KoJZz/Control-Rakatuy/testing/testing.kicad_sch

## KiCad design testing/testing.kicad_sch (2026-04-11)

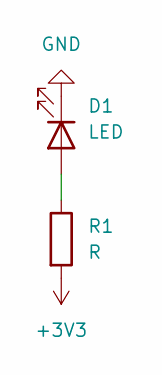
[picture p53: schematic testing.kicad_sch]

Parts:
D1: LED
R1: R

Connections:
+3V3: R1.2
GND: D1.1 (K)
unnamed: D1.2 (A), R1.1
