KoJZz/Control-Rakatuy/Firmware/FOCCube/Core/Src/main.c

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
/* Includes ------------------------------------------------------------------*/
#include "main.h"
#include "usb_device.h"

/* USER CODE BEGIN Includes */
#include "main.h"
#include "usb_device.h"
#include "usbd_cdc_if.h" // For CDC_Transmit_FS
#include "arm_math.h"
#include <stdbool.h>
#include <stdio.h>       // For snprintf
/* USER CODE END Includes */

ADC_HandleTypeDef hadc1;
ADC_HandleTypeDef hadc2;

TIM_HandleTypeDef htim1;
TIM_HandleTypeDef htim2;

/* USER CODE BEGIN PV */
extern volatile bool hardware_fault_latched;
extern volatile float32_t current_vbus_v;
extern volatile float32_t system_max_voltage;
extern volatile float32_t target_Id;
extern volatile float32_t target_Iq;
extern volatile float32_t offset_a;
extern volatile float32_t offset_c;

extern volatile float32_t I_q;
extern volatile float32_t I_d;
extern volatile float current_velocity_rad_s;
extern volatile float base_electrical_angle;

volatile float serial_commanded_current = 0.0f; // Stores the USB input


/* USER CODE END PV */

void SystemClock_Config(void);
static void MX_GPIO_Init(void);
static void MX_ADC1_Init(void);
static void MX_TIM1_Init(void);
static void MX_ADC2_Init(void);
static void MX_TIM2_Init(void);
/**
  * @brief  The application entry point.
  * @retval int
  */
int main(void)
{

  /* MCU Configuration--------------------------------------------------------*/

  /* Reset of all peripherals, Initializes the Flash interface and the Systick. */
  HAL_Init();

  /* Configure the system clock */
  SystemClock_Config();

  /* Initialize all configured peripherals */
  MX_GPIO_Init();
  MX_ADC1_Init();
  MX_TIM1_Init();
  MX_USB_DEVICE_Init();
  MX_ADC2_Init();
  MX_TIM2_Init();
  /* USER CODE BEGIN 2 */
  // 1. Enable Gate Driver
  HAL_GPIO_WritePin(EN_GATE_GPIO_Port, EN_GATE_Pin, GPIO_PIN_SET);
  HAL_Delay(10);

  // 2. Start ADCs
  HAL_ADCEx_InjectedStart(&hadc1);
  HAL_ADCEx_InjectedStart(&hadc2);

  // ==========================================
  // 3. DC CALIBRATION (Find true 0-Amp midpoint)
  // ==========================================
  HAL_GPIO_WritePin(EN_GATE_GPIO_Port, EN_GATE_Pin, GPIO_PIN_RESET);
  HAL_GPIO_WritePin(DC_CAL_GPIO_Port, DC_CAL_Pin, GPIO_PIN_SET);
  HAL_Delay(10);

  // CRITICAL FIX: Temporarily disable hardware triggers (JEXTEN = 00)
  // so the ADC respects our software JSWSTART command!
  hadc1.Instance->CR2 &= ~ADC_CR2_JEXTEN;
  hadc2.Instance->CR2 &= ~ADC_CR2_JEXTEN;

  uint32_t sum_a = 0, sum_c = 0;
  for(int i = 0; i < 1000; i++) {
	// Clear the JEOC flags BEFORE starting the conversion
	hadc1.Instance->SR = ~(ADC_SR_JEOC);
	hadc2.Instance->SR = ~(ADC_SR_JEOC);

	// Trigger BOTH ADCs manually
	SET_BIT(hadc1.Instance->CR2, ADC_CR2_JSWSTART);
	SET_BIT(hadc2.Instance->CR2, ADC_CR2_JSWSTART);

	while (!(hadc1.Instance->SR & ADC_SR_JEOC)) {}
	while (!(hadc2.Instance->SR & ADC_SR_JEOC)) {}

	sum_a += HAL_ADCEx_InjectedGetValue(&hadc1, ADC_INJECTED_RANK_1);
	sum_c += HAL_ADCEx_InjectedGetValue(&hadc2, ADC_INJECTED_RANK_1);
	HAL_Delay(1);
  }

  extern volatile float32_t offset_a;
  extern volatile float32_t offset_c;
  offset_a = (float32_t)sum_a / 1000.0f;
  offset_c = (float32_t)sum_c / 1000.0f;

  HAL_GPIO_WritePin(DC_CAL_GPIO_Port, DC_CAL_Pin, GPIO_PIN_RESET);
  HAL_GPIO_WritePin(EN_GATE_GPIO_Port, EN_GATE_Pin, GPIO_PIN_SET);
  HAL_Delay(10);

  // ==========================================
  // 4. INITIALIZE PWM AND HARDWARE TIMERS
  // ==========================================
  // Pre-center the PWM registers at 50% (0V output) before turning them on
  TIM1->CCR1 = 2099;
  TIM1->CCR2 = 2099;
  TIM1->CCR3 = 2099;

  HAL_TIM_PWM_Start(&htim1, TIM_CHANNEL_1);
  HAL_TIMEx_PWMN_Start(&htim1, TIM_CHANNEL_1);
  HAL_TIM_PWM_Start(&htim1, TIM_CHANNEL_2);
  HAL_TIMEx_PWMN_Start(&htim1, TIM_CHANNEL_2);
  HAL_TIM_PWM_Start(&htim1, TIM_CHANNEL_3);
  HAL_TIMEx_PWMN_Start(&htim1, TIM_CHANNEL_3);

  extern void Init_Rotor_Angle(void);
  Init_Rotor_Angle();
  HAL_TIM_Base_Start(&htim2);

  // ==========================================
  // 5. ARM THE FOC LOOP
  // ==========================================
  // CRITICAL FIX: Restore the hardware triggers to Rising Edge (JEXTEN = 01)
  // so TIM1_CC4 can physically trigger the ADCs again.
  hadc1.Instance->CR2 |= ADC_EXTERNALTRIGINJECCONVEDGE_RISING;
  hadc2.Instance->CR2 |= ADC_EXTERNALTRIGINJECCONVEDGE_RISING;

  // Stop the ADCs from software mode, then restart them in Hardware Trigger mode
  HAL_ADC_Stop(&hadc1);
  HAL_ADC_Stop(&hadc2);
  HAL_ADCEx_InjectedStart(&hadc2);
  HAL_ADCEx_InjectedStart_IT(&hadc1);       // ARMS THE 20kHz INTERRUPT
  HAL_TIM_PWM_Start(&htim1, TIM_CHANNEL_4); // STARTS FIRING THE ADC TRIGGER
  /* USER CODE END 2 */

  /* Infinite loop */
  /* USER CODE BEGIN WHILE */
  while (1)
  {
	uint16_t raw_throttle = 0;
	uint16_t raw_vbus = 0;
	// ========================================================
	// 1. POLL REGULAR ADC CHANNELS (Register-Level Multiplexing)
	// ========================================================
	uint32_t timeout;

	// Force the Sequence Length to exactly 1 conversion
	hadc1.Instance->SQR1 &= ~ADC_SQR1_L;

	// --- Read Throttle (Channel 5) ---
	hadc1.Instance->SQR3 = 5; // Tell the sequencer to only look at CH5
	SET_BIT(hadc1.Instance->CR2, ADC_CR2_SWSTART);

	timeout = 20000;
	while (!(hadc1.Instance->SR & ADC_SR_EOC) && --timeout) {}

	if (timeout > 0) {
	  raw_throttle = hadc1.Instance->DR;
	} else {
	  hadc1.Instance->SR = ~ADC_SR_OVR; // Clear Overrun if interrupted
	}

	// --- Read Battery Voltage (Channel 12) ---
	hadc1.Instance->SQR3 = 12; // Tell the sequencer to only look at CH12
	SET_BIT(hadc1.Instance->CR2, ADC_CR2_SWSTART);

	timeout = 20000;
	while (!(hadc1.Instance->SR & ADC_SR_EOC) && --timeout) {}

	if (timeout > 0) {
	  raw_vbus = hadc1.Instance->DR;

	  float32_t instant_vbus = (float32_t)raw_vbus * 0.015091f;
	  current_vbus_v = (current_vbus_v * 0.99f) + (instant_vbus * 0.01f);
	  system_max_voltage = current_vbus_v / 1.73205081f;
	} else {
	  hadc1.Instance->SR = ~ADC_SR_OVR;
	}

	// ========================================================
	// 3. THROTTLE MAPPING & SAFETY INTERLOCKS
	// ========================================================
	// TEST FLAGS: Change these during development
	bool bypass_deadman = true;

	static uint32_t fault_timer = 0;
	static bool in_fault_recovery = false;

	uint8_t deadman_pressed = (HAL_GPIO_ReadPin(DEADMAN_GPIO_Port, DEADMAN_Pin) == GPIO_PIN_RESET) || bypass_deadman;
	uint8_t voltage_safe = (current_vbus_v > 40.0f && current_vbus_v < 55.0f);

	// --- SCENARIO 1: HARDWARE FAULT DETECTED ---
	// We now read our software latch instead of the physical pin!
	uint8_t drv_faulted = hardware_fault_latched;

	if (drv_faulted || in_fault_recovery)
	{
	  target_Iq = 0.0f; // Immediately kill software torque
	  HAL_GPIO_WritePin(LED_GREEN_GPIO_Port, LED_GREEN_Pin, GPIO_PIN_RESET);
	  HAL_GPIO_WritePin(LED_RED_GPIO_Port, LED_RED_Pin, GPIO_PIN_SET);

	  if (!in_fault_recovery) {
		  fault_timer = HAL_GetTick();
		  in_fault_recovery = true;
	  }
	  else if (HAL_GetTick() - fault_timer > 2000) {

		  extern void Reset_FOC_Integrators(void);
		  Reset_FOC_Integrators();

		  extern void Init_Rotor_Angle(void);
		  Init_Rotor_Angle();

		  // --- WAKE UP SEQUENCE ---
		  hardware_fault_latched = false;                 // 1. Clear the latch
		  TIM1->BDTR |= TIM_BDTR_MOE;                     // 2. Restore PWM outputs
		  HAL_GPIO_WritePin(EN_GATE_GPIO_Port, EN_GATE_Pin, GPIO_PIN_SET); // 3. Enable Gates

		  in_fault_recovery = false;
	  }
	}
	// --- SCENARIO 2: SYSTEM NORMAL & ARMED ---
	else if (deadman_pressed && voltage_safe)
	{
	  HAL_GPIO_WritePin(LED_GREEN_GPIO_Port, LED_GREEN_Pin, GPIO_PIN_SET);
	  HAL_GPIO_WritePin(LED_RED_GPIO_Port, LED_RED_Pin, GPIO_PIN_RESET);

	  /* --- TEMPORARILY DISABLED FOR SERIAL BENCH TEST ---
	  float32_t commanded_current = 0.0f;
	  if (raw_throttle > 1000) {
		  commanded_current = ((float32_t)(raw_throttle - 1000) / 2000.0f) * 20.0f;
		  if (commanded_current > 20.0f) commanded_current = 20.0f;
	  }
	  target_Iq = commanded_current;
	  --------------------------------------------------- */

	  target_Iq = serial_commanded_current; // Feed FOC from USB instead
	}
	// --- SCENARIO 3: SYSTEM SAFE (IDLE) ---
	else
	{
	  HAL_GPIO_WritePin(LED_GREEN_GPIO_Port, LED_GREEN_Pin, GPIO_PIN_RESET);
	  HAL_GPIO_WritePin(LED_RED_GPIO_Port, LED_RED_Pin, GPIO_PIN_SET);
	  target_Iq = 0.0f;
	}
	// ========================================================
	// 4. USB TELEMETRY STREAM (10Hz)
	// ========================================================
	static uint32_t last_print_time = 0;

	// Print every 100ms so it is readable by a human
	if (HAL_GetTick() - last_print_time >= 100)
	{
	  last_print_time = HAL_GetTick();

	  // Create a character buffer to hold the formatted string
	  static char telemetry_buffer[128];

	  // Format the string with your live FOC metrics
	  // \r\n acts as the "Enter" key for the serial terminal
	  uint16_t len = snprintf(telemetry_buffer, sizeof(telemetry_buffer),
							  "Vbus:%5.1fV | RPM:%6.0f | Tgt:%5.2fA | Iq:%5.2fA | Id:%5.2fA\r\n",
							  current_vbus_v,
							  (current_velocity_rad_s * 9.549297f) / POLE_PAIRS, // Convert rad/s to mechanical RPM
							  target_Iq,
							  I_q,
							  I_d);

	  // Fire it out of the USB port
	  CDC_Transmit_FS((uint8_t*)telemetry_buffer, len);
	}
	// Run the main loop at roughly 100Hz (10ms).
	// This saves CPU power. The FOC interrupt still runs perfectly at 20kHz!
	HAL_Delay(10);
    /* USER CODE END WHILE */

    /* USER CODE BEGIN 3 */
  }
  /* USER CODE END 3 */
}

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
/**
  * @brief  Period elapsed callback in non blocking mode
  * @note   This function is called  when TIM6 interrupt took place, inside
  * HAL_TIM_IRQHandler(). It makes a direct call to HAL_IncTick() to increment
  * a global variable "uwTick" used as application time base.
  * @param  htim : TIM handle
  * @retval None
  */
void HAL_TIM_PeriodElapsedCallback(TIM_HandleTypeDef *htim)
{
  if (htim->Instance == TIM6)
  {
    HAL_IncTick();
  }
}

/**
  * @brief  This function is executed in case of error occurrence.
  * @retval None
  */
void Error_Handler(void)
{
  /* USER CODE BEGIN Error_Handler_Debug */
  /* User can add his own implementation to report the HAL error return state */
  __disable_irq();
  while (1)
  {
  }
  /* USER CODE END Error_Handler_Debug */
}
#ifdef USE_FULL_ASSERT
/**
  * @brief  Reports the name of the source file and the source line number
  *         where the assert_param error has occurred.
  * @param  file: pointer to the source file name
  * @param  line: assert_param error line source number
  * @retval None
  */
void assert_failed(uint8_t *file, uint32_t line)
{
  /* USER CODE BEGIN 6 */
  /* User can add his own implementation to report the file name and line number,
     ex: printf("Wrong parameters value: file %s on line %d\r\n", file, line) */
  /* USER CODE END 6 */
}
#endif /* USE_FULL_ASSERT */
