KoJZz/Control-Rakatuy/Firmware/EasySTMz/src/peripheral_overrides.c

#include "Arduino.h"
#include "PeripheralPins.h"

// ============================================================================
// CUSTOM TIM1-LOCKED PERIPHERAL TIMERS FOR VESC 4.12 (STM32F405RG)
// ============================================================================
// Explicit override mapping parameters to isolate high-side and low-side pins
// strictly onto TIM1, avoiding hardware execution library conflicts.
// ============================================================================
// ============================================================================
// HARDWARE TIMER MAP (TIM1 ONLY FOR HIGH-SIDES)
// ============================================================================
const PinMap PinMap_TIM[] = {
  // --- Core Phase High-Side Channels (TIM1) ---
  {PA_8,  TIM1,   STM_PIN_DATA_EXT(STM_MODE_AF_PP, GPIO_PULLUP, GPIO_AF1_TIM1, 1, 0)}, // TIM1_CH1 (H3 / Phase C High)
  {PA_9,  TIM1,   STM_PIN_DATA_EXT(STM_MODE_AF_PP, GPIO_PULLUP, GPIO_AF1_TIM1, 2, 0)}, // TIM1_CH2 (H2 / Phase B High)
  {PA_10, TIM1,   STM_PIN_DATA_EXT(STM_MODE_AF_PP, GPIO_PULLUP, GPIO_AF1_TIM1, 3, 0)}, // TIM1_CH3 (H1 / Phase A High)

  // --- Auxiliary Generic Timers Layout ---
//   {PA_0,  TIM2,   STM_PIN_DATA_EXT(STM_MODE_AF_PP, GPIO_PULLUP, GPIO_AF1_TIM2, 1, 0)}, 
//   {PA_1,  TIM5,   STM_PIN_DATA_EXT(STM_MODE_AF_PP, GPIO_PULLUP, GPIO_AF2_TIM5, 2, 0)}, 
//   {PA_2,  TIM5,   STM_PIN_DATA_EXT(STM_MODE_AF_PP, GPIO_PULLUP, GPIO_AF2_TIM5, 3, 0)}, 
  {PA_3,  TIM5,   STM_PIN_DATA_EXT(STM_MODE_AF_PP, GPIO_PULLUP, GPIO_AF2_TIM5, 4, 0)}, 
  // {PA_5,  TIM2,   STM_PIN_DATA_EXT(STM_MODE_AF_PP, GPIO_PULLUP, GPIO_AF1_TIM2, 1, 0)}, 
  {PA_6,  TIM13,  STM_PIN_DATA_EXT(STM_MODE_AF_PP, GPIO_PULLUP, GPIO_AF9_TIM13, 1, 0)}, 
  {PA_7,  TIM14,  STM_PIN_DATA_EXT(STM_MODE_AF_PP, GPIO_PULLUP, GPIO_AF9_TIM14, 1, 0)}, 
  {PB_3,  TIM2,   STM_PIN_DATA_EXT(STM_MODE_AF_PP, GPIO_PULLUP, GPIO_AF1_TIM2, 2, 0)}, 
  {PB_4,  TIM3,   STM_PIN_DATA_EXT(STM_MODE_AF_PP, GPIO_PULLUP, GPIO_AF2_TIM3, 1, 0)}, 
  {PB_5,  TIM3,   STM_PIN_DATA_EXT(STM_MODE_AF_PP, GPIO_PULLUP, GPIO_AF2_TIM3, 2, 0)}, 
  {PB_6,  TIM4,   STM_PIN_DATA_EXT(STM_MODE_AF_PP, GPIO_PULLUP, GPIO_AF2_TIM4, 1, 0)}, 
  {PB_7,  TIM4,   STM_PIN_DATA_EXT(STM_MODE_AF_PP, GPIO_PULLUP, GPIO_AF2_TIM4, 2, 0)}, 
  {PB_8,  TIM4,   STM_PIN_DATA_EXT(STM_MODE_AF_PP, GPIO_PULLUP, GPIO_AF2_TIM4, 3, 0)}, 
  {PB_9,  TIM4,   STM_PIN_DATA_EXT(STM_MODE_AF_PP, GPIO_PULLUP, GPIO_AF2_TIM4, 4, 0)}, 
  {PC_6,  TIM3,   STM_PIN_DATA_EXT(STM_MODE_AF_PP, GPIO_PULLUP, GPIO_AF2_TIM3, 1, 0)}, 
  {PC_7,  TIM8,   STM_PIN_DATA_EXT(STM_MODE_AF_PP, GPIO_PULLUP, GPIO_AF3_TIM8, 2, 0)}, 
  {PC_8,  TIM3,   STM_PIN_DATA_EXT(STM_MODE_AF_PP, GPIO_PULLUP, GPIO_AF2_TIM3, 3, 0)}, 
  {PC_9,  TIM8,   STM_PIN_DATA_EXT(STM_MODE_AF_PP, GPIO_PULLUP, GPIO_AF3_TIM8, 4, 0)}, 

  {NC,    NULL,   0} // End marker
};

// // ============================================================================
// // CUSTOM PERIPHERAL ADC MAP FOR VESC 4.12 (STM32F405RG)
// // ============================================================================
// // Overrides the weak core definitions. Isolates exactly the pins needed 
// // for your shunts, voltage divider, and throttle lines using ADC1.
// // ============================================================================
// const PinMap PinMap_ADC[] = {
//   // --- Current Sense Channels (Bi-directional Shunts) ---
//   {PB_0,  ADC1,   STM_PIN_DATA_EXT(STM_MODE_ANALOG, GPIO_NOPULL, 0, 8, 0)},  // ADC1_IN8  (PIN_CURR_C)
//   {PB_1,  ADC1,   STM_PIN_DATA_EXT(STM_MODE_ANALOG, GPIO_NOPULL, 0, 9, 0)},  // ADC1_IN9  (PIN_CURR_A)

//   // --- Bus Voltage Monitor (Divider Rail) ---
//   {PC_2,  ADC1,   STM_PIN_DATA_EXT(STM_MODE_ANALOG, GPIO_NOPULL, 0, 12, 0)}, // ADC1_IN12 (PIN_VIN_SENSE)

//   // --- User Throttle Input ---
//   {PA_5,  ADC1,   STM_PIN_DATA_EXT(STM_MODE_ANALOG, GPIO_NOPULL, 0, 5, 0)},  // ADC1_IN5  (PIN_THROTTLE)

//   {NC,    NP,     0} // Termination guard indicator for the core framework loop
// };
